OLIMEX/FOSDEM-MUSIC-BOX/SOFTWARE/FOSDEM_Music_Box_Demo/Notes.c

#include "Notes.h"
#include <avr/pgmspace.h>

// https://www.seventhstring.com/resources/notefrequencies.html
const int NoteFrequency[] PROGMEM =   
{
	0, // pause
/*  note  c  cS/dB    d  dS/eB    e     f  fS/gB    g  gS/aB    a  aS/bB    b
octave*/
/*0*/    16,   17,   18,   19,   21,   22,   23,   25,   26,   28,   29,   31,
/*1*/    33,   35,   37,   39,   41,   44,   46,   49,   52,   55,   58,   62,
/*2*/    65,   70,   73,   78,   82,   87,   93,   98,  104,  110,  117,  124,
/*3*/   131,  139,  147,  156,  165,  175,  185,  196,  208,  220,  233,  247,
/*4*/   261,  277,  294,  311,  329,  349,  370,  392,  415,  440,  466,  494,
/*5*/   523,  554,  587,  622,  659,  699,  740,  784,  831,  880,  932,  988,
/*6*/  1047, 1109, 1175, 1245, 1319, 1397, 1480, 1568, 1661, 1760, 1865, 1976,
/*7*/  2093, 2217, 2349, 2489, 2637, 2794, 2960, 3136, 3322, 3520, 3729, 3951,
/*8*/  4186, 4435, 4699, 4978, 5274, 5588, 5920, 6272, 6645, 7040, 7459, 7902,
};
