OLIMEX/FOSDEM-MUSIC-BOX/SOFTWARE/FOSDEM_Music_Box_Demo/Tracks/Ode_of_Joy.h

//https://www.8notes.com/scores/10433.asp
#ifndef	_ODE_OF_JOY_H
#define	_ODE_OF_JOY_H


#include "../Notes.h"

int OOJ1_Tempo = 140;
const int OOJ1_NoteC0[] PROGMEM =   {_c5 , _c5 , _d5, _g4,	_e5, _d5, _c5 , _g4,	_e4, _e4, _g4, _c5 ,	_c5 , _g4, _g4, _END};
const int OOJ1_NoteC1[] PROGMEM =   {_e5 , _e5 , _f5, _g5,	_g5, _f5, _e5 , _d5,	_c5, _c5, _d5, _e5 ,	_e5 , _d5, _d5, _END};
const int OOJ1_NoteC2[] PROGMEM =   {_fS6, _fS6, _g6, _a6,	_a6, _g6, _fS6, _e6,	_d6, _d6, _e6, _fS6,	_fS6, _e6, _e6, _END};
const int OOJ1_Duration[] PROGMEM = {_4  , _4  , _4 , _4 ,	_4 , _4 , _4  , _4 ,	_4 , _4 , _4 , _4  ,	_4D , _8 , _2 , _END};

int OOJ2_Tempo = 140;
const int OOJ2_NoteC0[] PROGMEM =   {_c5 , _c5 , _d5, _g4,	_e5, _d5, _c5 , _g4,	_e4, _e4, _g4, _c5 ,	_b4, _g4, _g4, _c5, _END};
const int OOJ2_NoteC1[] PROGMEM =   {_e5 , _e5 , _f5, _g5,	_g5, _f5, _e5 , _d5,	_c5, _c5, _d5, _e5 ,	_d5, _d5, _c5, _c5, _END};
const int OOJ2_NoteC2[] PROGMEM =   {_fS6, _fS6, _g6, _a6,	_a6, _g6, _fS6, _e6,	_d6, _d6, _e6, _fS6,	_e6, _e6, _d6, _d6, _END};
const int OOJ2_Duration[] PROGMEM = {_4  , _4  , _4 , _4 ,	_4 , _4 , _4  , _4 ,	_4 , _4 , _4 , _4  ,	_4 , _8 , _8 , _2 , _END};

int OOJ3_Tempo = 140;
const int OOJ3_NoteC0[] PROGMEM =   {_g4, _g4, _g4 , _g4,	_g4, _g4 , _g4, _g4 , _g4,	_g4, _g4 , _g4, _gS4, _gS4,		_a4, _fS4, _g4, _c5 , _END};
const int OOJ3_NoteC1[] PROGMEM =   {_d5, _d5, _e5 , _c5,	_d5, _e5 , _f5, _e5 , _c5,	_d5, _e5 , _f5, _e5 , _d5 ,		_c5, _d5 , _g4, _e5 , _END};
const int OOJ3_NoteC2[] PROGMEM =   {_e6, _e6, _fS6, _d6,	_e6, _fS6, _g6, _fS6, _d6,	_e6, _fS6, _g6, _fS6, _e6 ,		_d6, _e6 , _a5, _fS6, _END};
const int OOJ3_Duration[] PROGMEM = {_4 , _4 , _4  , _4 ,	_4 , _8  , _8 , _4  , _4 ,	_4 , _8  , _8 , _4  , _4  ,		_4 , _4  , _4 , _4  , _END};

int OOJ4_Tempo = 140;
const int OOJ4_NoteC0[] PROGMEM =   {_b4 , _b4 , _aB4, _aB4,	_e4, _e4, _f4 , _f4,	_e4, _e4, _g4, _c5 ,	_b4, _g4, _g4, _c5, _END};
const int OOJ4_NoteC1[] PROGMEM =   {_e5 , _e5 , _f5 , _g5 ,	_g5, _f5, _e5 , _d5,	_c5, _c5, _d5, _e5 ,	_d5, _d5, _c5, _c5, _END};
const int OOJ4_NoteC2[] PROGMEM =   {_fS6, _fS6, _g6 , _a6 ,	_a6, _g6, _fS6, _e6,	_d6, _d6, _e6, _fS6,	_e6, _e6, _d6, _d6, _END};
const int OOJ4_Duration[] PROGMEM = {_4  , _4  , _4  , _4  ,	_4 , _4 , _4  , _4 ,	_4 , _4 , _4 , _4  ,	_4 , _8 , _8 , _2 , _END};

#endif
