OLIMEX/FOSDEM-MUSIC-BOX/SOFTWARE/FOSDEM_Music_Box_Demo_PWM/Tracks/Test.h

#ifndef	_TEST_H
#define	_TEST_H

#include "../Notes.h"

int Test1_Tempo = 120;
const int Test1_Note[] PROGMEM =
{
	_c2, _cS2, _d2, _eB2, _e2, _f2, _fS2, _g2, _gS2, _a2, _bB2, _b2,
	_c3, _cS3, _d3, _eB3, _e3, _f3, _fS3, _g3, _gS3, _a3, _bB3, _b3,
	_c4, _cS4, _d4, _eB4, _e4, _f4, _fS4, _g4, _gS4, _a4, _bB4, _b4,
	_c5, _cS5, _d5, _eB5, _e5, _f5, _fS5, _g5, _gS5, _a5, _bB5, _b5,
	_c6, _cS6, _d6, _eB6, _e6, _f6, _fS6, _g6, _gS6, _a6, _bB6, _b6,
	_c7, _cS7, _d7, _eB7, _e7, _f7, _fS7, _g7, _gS7, _a7, _bB7, _b7,
	_c8, _cS8, _d8, _eB8, _e8, _f8, _fS8, _g8, _gS8, _a8, _bB8, _b8,
	_END
};

const int Test1_Duration[] PROGMEM =
{
	_2, _8, _8, _8, _4, _8, _8, _8, _4, _8, _8, _8,
	_2, _8, _8, _8, _4, _8, _8, _8, _4, _8, _8, _8,
	_2, _8, _8, _8, _4, _8, _8, _8, _4, _8, _8, _8,
	_2, _8, _8, _8, _4, _8, _8, _8, _4, _8, _8, _8,
	_2, _8, _8, _8, _4, _8, _8, _8, _4, _8, _8, _8,
	_2, _8, _8, _8, _4, _8, _8, _8, _4, _8, _8, _8,
	_2, _8, _8, _8, _4, _8, _8, _8, _4, _8, _8, _8,
	_END
};

#endif
